kalanda/photoduino/hardware/photoduino.solenoid.valve.interface.1.0/pdf/photoduino.solenoid.valve.interface.v.1.0.schema.pdf

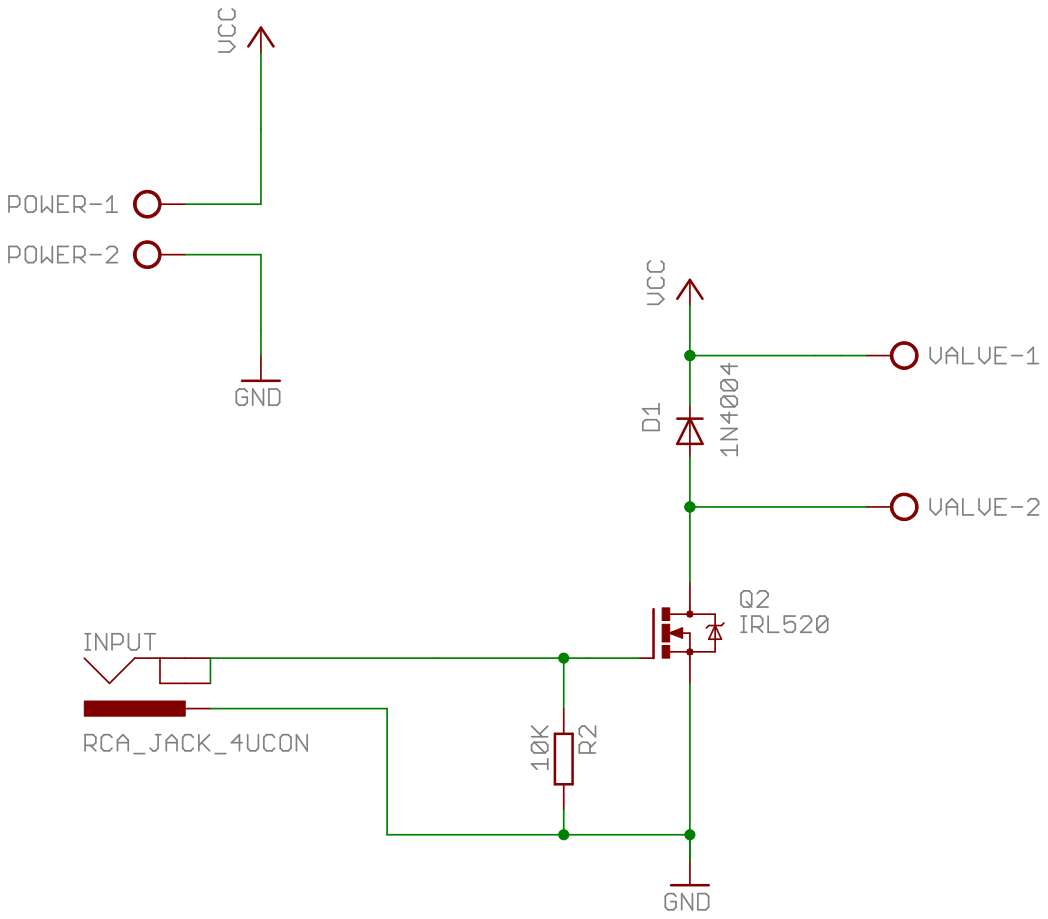
[picture p14: page 1]
