kalanda/photoduino/hardware/photoduino.solenoid.valve.interface.1.0/pdf/photoduino.solenoid.valve.interface.v.1.0.silk-layer.pdf

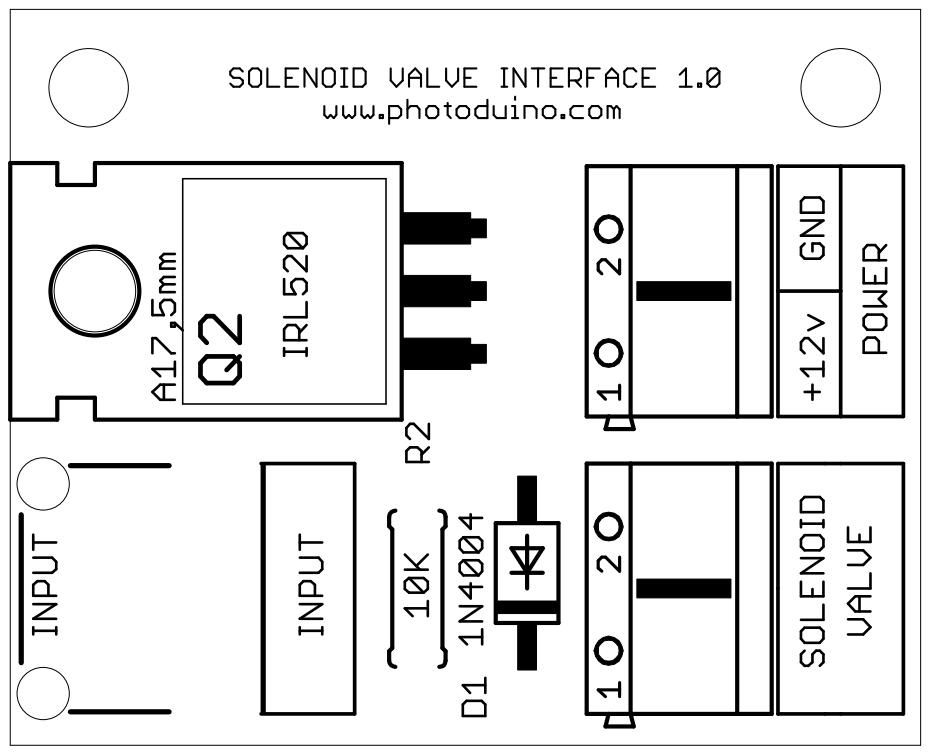
[picture p15: page 1]
