kalanda/photoduino/firmware/Photoduino/language_FR.h

/*
 * This file is part of Photoduino.
 *
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
 * Fichier francais cree par Guy RENOU le 25 mai 2012.
 * guy.renou@free.fr
 */
 
 // Messages list                                                 "123456789012345"
const prog_char PROGMEM MSG_LANGUAGE_CODE[] =                     "FR";
const prog_char PROGMEM MSG_PHOTODUINO_V[] =                      "Photoduino v";
const prog_char PROGMEM MSG_READY[] =                             "Tests OK Pret !";
const prog_char PROGMEM MSG_MAIN_MENU[] =                         "Menu principal";
const prog_char PROGMEM MSG_SYSTEM_CONFIG[] =                     "Config. systeme";
const prog_char PROGMEM MSG_INTERVALOMETER[] =                    "Intervalometre";
const prog_char PROGMEM MSG_SENSOR_TRIGGER[] =                    "Mode capteur";
const prog_char PROGMEM MSG_CONFIG[] =                            "Configuration";
const prog_char PROGMEM MSG_CONFIG_TRIGGER[] =                    "Type de capteur";
const prog_char PROGMEM MSG_CONFIG_DROPS[] =                      "Config. gouttes";
const prog_char PROGMEM MSG_RUN[] =                               "Action !!!";
const prog_char PROGMEM MSG_RUNNING[] =                           "Action en cours...";
const prog_char PROGMEM MSG_RESET_CONFIG[] =                      "Reinitialisation";
const prog_char PROGMEM MSG_AUTOFOCUS_TIME[] =                    "Temps Autofocus";
const prog_char PROGMEM MSG_SHUTTERLAG_TIME[] =                   "Temps shutterlag";
const prog_char PROGMEM MSG_USE_FLASH1[] =                        "Flash1";
const prog_char PROGMEM MSG_USE_FLASH2[] =                        "Flash2";
const prog_char PROGMEM MSG_FLASH1_PRETIME[] =                    "Temps Flash1";
const prog_char PROGMEM MSG_FLASH2_PRETIME[] =                    "Temps Flash2";
const prog_char PROGMEM MSG_CLOSE_PRETIME[] =                     "Delais d'arret";
const prog_char PROGMEM MSG_INTERVAL_UNITS[] =                    "Unite Intervalle";
const prog_char PROGMEM MSG_INTERVAL_VALUE[] =                    "Temps Intervalle";
const prog_char PROGMEM MSG_CYCLES[] =                            "Nb prises de vue";
const prog_char PROGMEM MSG_SENSOR[] =                            "Actif";
const prog_char PROGMEM MSG_SENSOR_LIMIT[] =                      "Reglage sensibil";
const prog_char PROGMEM MSG_SENSOR_VALUE[] =                      "Capteur :";
const prog_char PROGMEM MSG_LIMIT_VALUE[] =                       "Sensibilite :";
const prog_char PROGMEM MSG_SHOOTING_MODE[] =                     "Mode prise de vue";
const prog_char PROGMEM MSG_INTERCYCLE_TIME[] =                   "T. entre Prises";
const prog_char PROGMEM MSG_BACKLIGHT[] =                         "Afficheur";
const prog_char PROGMEM MSG_SPEAKER[] =                           "Buzzer";
const prog_char PROGMEM MSG_RESETTING[] =                         "Reinitialisation";
const prog_char PROGMEM MSG_ABORTING[] =                          "Abandon ...";
const prog_char PROGMEM MSG_YES[] =                               "OUI";
const prog_char PROGMEM MSG_NO[] =                                "NON";
const prog_char PROGMEM MSG_NONE[] =                              "Aucun";
const prog_char PROGMEM MSG_UNITS_US[] =                          "us";
const prog_char PROGMEM MSG_UNITS_MS[] =                          "ms";
const prog_char PROGMEM MSG_UNITS_SECS[] =                        "Secondes";
const prog_char PROGMEM MSG_UNITS_MINS[] =                        "Minutes";
const prog_char PROGMEM MSG_UNITS_HOURS[] =                       "Heures";
const prog_char PROGMEM MSG_UNITS_DAYS[] =                        "Jours";
const prog_char PROGMEM MSG_UNITS_CYCLES[] =                      "Prises";
const prog_char PROGMEM MSG_UNITS_DROPS[] =                       "Gouttes";
const prog_char PROGMEM MSG_SHOOTINGMODE_NORMAL[] =               "Normale";
const prog_char PROGMEM MSG_SHOOTINGMODE_PREBULB[] =              "Pause - Bulb";
const prog_char PROGMEM MSG_SHOOTINGMODE_MIRRORLOCKUP[] =         "Mirroir releve";
const prog_char PROGMEM MSG_SENSOR_TUNING[] =                     "Tuning capteurs";
const prog_char PROGMEM MSG_SENSOR_TUNING_VISUAL[] =              "Bargraphe";
const prog_char PROGMEM MSG_SENSOR_TUNING_NUMERIC[] =             "Numerique";
const prog_char PROGMEM MSG_SENSOR_TYPE[] =                       "Type capteur";
const prog_char PROGMEM MSG_SENSOR_TYPE_AUDIO[] =                 "Son";
const prog_char PROGMEM MSG_SENSOR_TYPE_BARRIER[] =               "Barriere";
const prog_char PROGMEM MSG_SENSOR_TYPE_SHOCK[] =                 "Choc";
const prog_char PROGMEM MSG_SENSOR_TYPE_LIGHT[] =                 "Lumiere";
const prog_char PROGMEM MSG_MIRROR_LOCKUP_TIMEOUT[] =             "Timeout mirroir";
const prog_char PROGMEM MSG_DEVICE_PORT_TYPE[] =                  "Type dispositif";
const prog_char PROGMEM MSG_DEVICE_PORT_TYPE_LASER[] =            "Laser";
const prog_char PROGMEM MSG_DEVICE_PORT_TYPE_SOLENOID_VALVE[] =   "Electrovanne";
const prog_char PROGMEM MSG_DROPS_COUNT[] =                       "Nombre gouttes";
const prog_char PROGMEM MSG_DROPS_DURATION[] =                    "Grosseur goutte";
const prog_char PROGMEM MSG_DROPS_INTERVAL[] =                    "T. entre gouttes";
const prog_char PROGMEM MSG_REMOTE_MODE[] =                       "Mode Remote";
