kalanda/photoduino/firmware/Photoduino/language_IT.h

/*
 * This file is part of Photoduino.
 *
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
 * You should have received a copy of the GNU General Public License
 * along with Photoduino.  If not, see <http://www.gnu.org/licenses/>.
 */
 
 // Messages list                                                 "123456789012345"
const prog_char PROGMEM MSG_LANGUAGE_CODE[] =                     "IT";
const prog_char PROGMEM MSG_PHOTODUINO_V[] =                      "Photoduino v";
const prog_char PROGMEM MSG_READY[] =                             "Pronto!";
const prog_char PROGMEM MSG_MAIN_MENU[] =                         "Menu Principale";
const prog_char PROGMEM MSG_SYSTEM_CONFIG[] =                     "Config Sistema";
const prog_char PROGMEM MSG_INTERVALOMETER[] =                    "Intervallometro";
const prog_char PROGMEM MSG_SENSOR_TRIGGER[] =                    "Sensore Scatto";
const prog_char PROGMEM MSG_CONFIG[] =                            "Configurazione";
const prog_char PROGMEM MSG_CONFIG_TRIGGER[] =                    "Config Scatto";
const prog_char PROGMEM MSG_CONFIG_DROPS[] =                      "Config Gocce";
const prog_char PROGMEM MSG_RUN[] =                               "Esegui";
const prog_char PROGMEM MSG_RUNNING[] =                           "In esecuzione...";
const prog_char PROGMEM MSG_RESET_CONFIG[] =                      "Reset Config";
const prog_char PROGMEM MSG_AUTOFOCUS_TIME[] =                    "Tempo Autofocus";
const prog_char PROGMEM MSG_SHUTTERLAG_TIME[] =                   "Rit. Otturatore";
const prog_char PROGMEM MSG_USE_FLASH1[] =                        "Usa Flash 1";
const prog_char PROGMEM MSG_USE_FLASH2[] =                        "Usa Flash 2";
const prog_char PROGMEM MSG_FLASH1_PRETIME[] =                    "ms Pre-Flash 1";
const prog_char PROGMEM MSG_FLASH2_PRETIME[] =                    "ms Pre-Flash 2";
const prog_char PROGMEM MSG_CLOSE_PRETIME[] =                     "ms Pre-Chiusura";
const prog_char PROGMEM MSG_INTERVAL_UNITS[] =                    "Unita Intervallo";
const prog_char PROGMEM MSG_INTERVAL_VALUE[] =                    "Val. Intervallo";
const prog_char PROGMEM MSG_CYCLES[] =                            "Cicli";
const prog_char PROGMEM MSG_SENSOR[] =                            "Sensore";
const prog_char PROGMEM MSG_SENSOR_LIMIT[] =                      "Limite Sensore";
const prog_char PROGMEM MSG_SENSOR_VALUE[] =                      ">Sensore :";
const prog_char PROGMEM MSG_LIMIT_VALUE[] =                       ">Limite  :";
const prog_char PROGMEM MSG_SHOOTING_MODE[] =                     "Modalita Scatto";
const prog_char PROGMEM MSG_INTERCYCLE_TIME[] =                   "Intervallo Cicli";
const prog_char PROGMEM MSG_BACKLIGHT[] =                         "Luce LCD";
const prog_char PROGMEM MSG_SPEAKER[] =                           "Suoni";
const prog_char PROGMEM MSG_RESETTING[] =                         "Ripristino...";
const prog_char PROGMEM MSG_ABORTING[] =                          "Annullamento...";
const prog_char PROGMEM MSG_YES[] =                               "SI";
const prog_char PROGMEM MSG_NO[] =                                "NO";
const prog_char PROGMEM MSG_NONE[] =                              "Nessuno";
const prog_char PROGMEM MSG_UNITS_US[] =                          "us";
const prog_char PROGMEM MSG_UNITS_MS[] =                          "ms";
const prog_char PROGMEM MSG_UNITS_SECS[] =                        "Secondi";
const prog_char PROGMEM MSG_UNITS_MINS[] =                        "Minuti";
const prog_char PROGMEM MSG_UNITS_HOURS[] =                       "Ore";
const prog_char PROGMEM MSG_UNITS_DAYS[] =                        "Giorni";
const prog_char PROGMEM MSG_UNITS_CYCLES[] =                      "Cicli";
const prog_char PROGMEM MSG_UNITS_DROPS[] =                       "Gocce";
const prog_char PROGMEM MSG_SHOOTINGMODE_NORMAL[] =               "Normale";
const prog_char PROGMEM MSG_SHOOTINGMODE_PREBULB[] =              "Modo Pre-Bulb";
const prog_char PROGMEM MSG_SHOOTINGMODE_MIRRORLOCKUP[] =         "Blocco Specchio";
const prog_char PROGMEM MSG_SENSOR_TUNING[] =                     "Tuning Sensore";
const prog_char PROGMEM MSG_SENSOR_TUNING_VISUAL[] =              "Visuale";
const prog_char PROGMEM MSG_SENSOR_TUNING_NUMERIC[] =             "Numerico";
const prog_char PROGMEM MSG_SENSOR_TYPE[] =                       "Tipo Sensore";
const prog_char PROGMEM MSG_SENSOR_TYPE_AUDIO[] =                 "Audio";
const prog_char PROGMEM MSG_SENSOR_TYPE_BARRIER[] =               "Barriera";
const prog_char PROGMEM MSG_SENSOR_TYPE_SHOCK[] =                 "Impatto";
const prog_char PROGMEM MSG_SENSOR_TYPE_LIGHT[] =                 "Luce";
const prog_char PROGMEM MSG_MIRROR_LOCKUP_TIMEOUT[] =             "Timeout Specchio";
const prog_char PROGMEM MSG_DEVICE_PORT_TYPE[] =                  "Tipo Device";
const prog_char PROGMEM MSG_DEVICE_PORT_TYPE_LASER[] =            "Laser";
const prog_char PROGMEM MSG_DEVICE_PORT_TYPE_SOLENOID_VALVE[] =   "Elettrovalvola";
const prog_char PROGMEM MSG_DROPS_COUNT[] =                       "Numero Gocce";
const prog_char PROGMEM MSG_DROPS_DURATION[] =                    "Durata Gocce";
const prog_char PROGMEM MSG_DROPS_INTERVAL[] =                    "Intervallo Gocce";
const prog_char PROGMEM MSG_REMOTE_MODE[] =                       "Modalita Remota";
